DetroitDartworks/Flycore/DDW Angled Noidcore/ATNC - Pusher Guide.stl

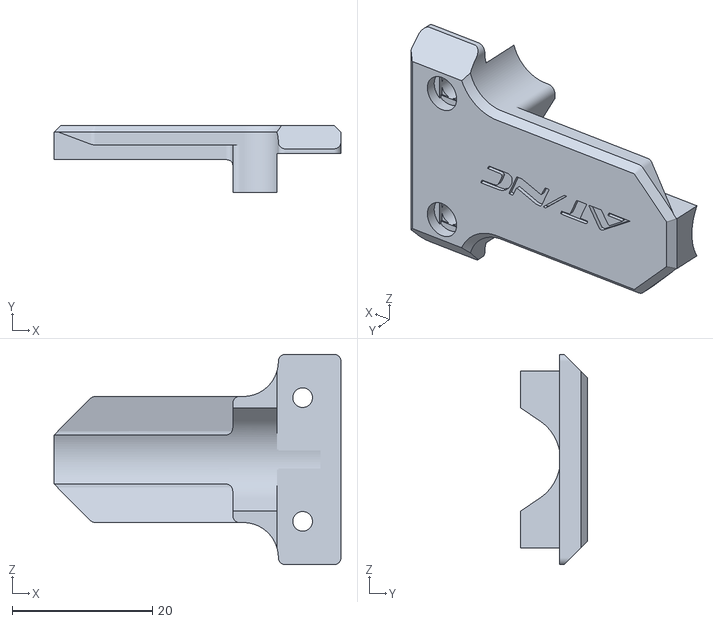
[picture p4: CAD file, 2025-03-11]
DDW Angled Noidcore/ATNC - Pusher Guide.stl
40.9 x 9.50 x 30.0
