DetroitDartworks/Flycore/FJZ05 Noidcore/FJZ05 Solenoid Flycore - HURR 33mm.stl

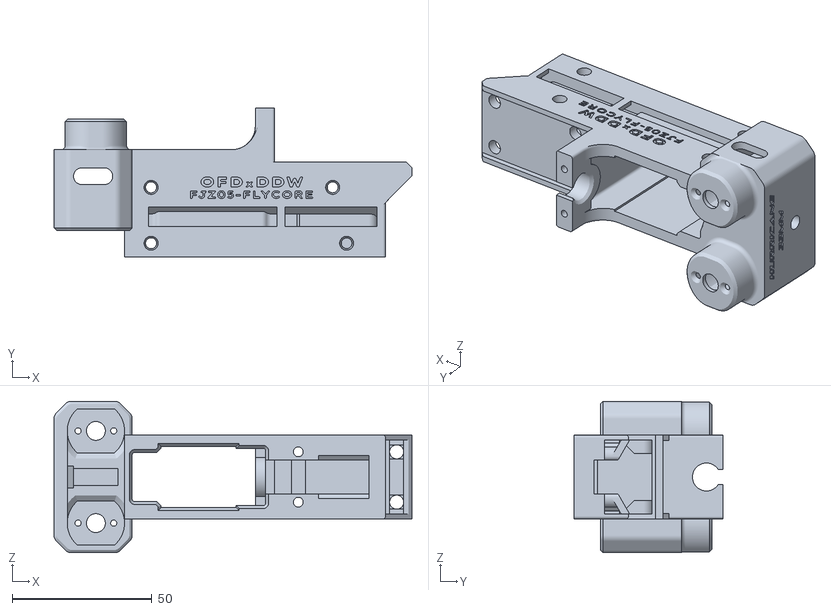
[picture p5: CAD file, 2024-03-11]
FJZ05 Noidcore/FJZ05 Solenoid Flycore - HURR 33mm.stl
128.2 x 53.5 x 54.2
