DetroitDartworks/Flycore/Gearcore v1/STEPs/Gearcore v1/GEARCORE_Trigger_Linkage_Reference.step

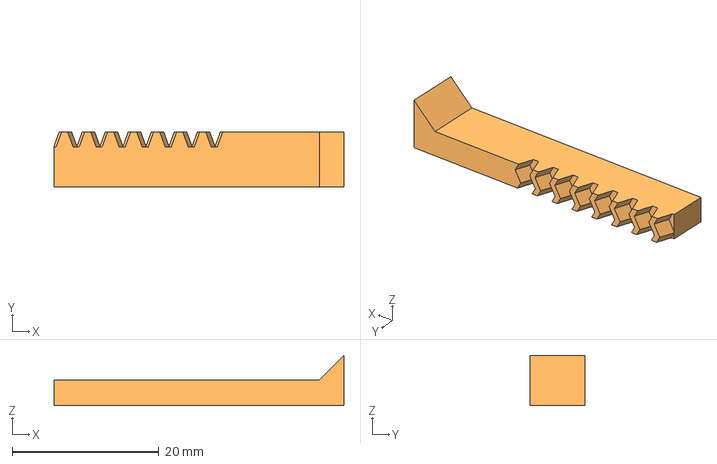
[picture p6: CAD file, 2025-07-15]
Gearcore v1/STEPs/Gearcore v1/GEARCORE_Trigger_Linkage_Reference.step
39.6 x 7.47 x 6.82 mm
