DetroitDartworks/Flycore/Gearcore v1/STLs/Gearcore v1/GearCore v1 - OFD_DDW_GEARCORE_STRAIGHT_NGALE_19.8MM_V1.stl

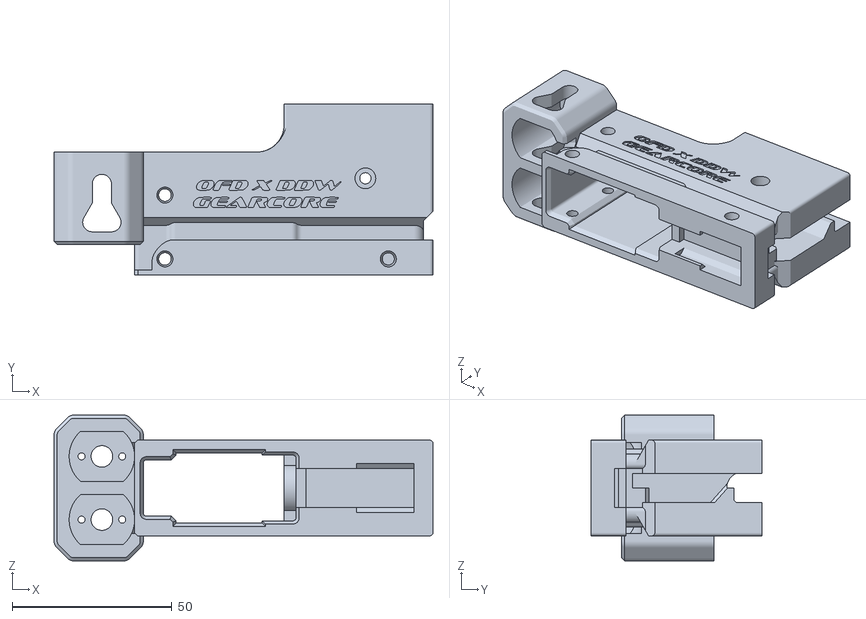
[picture p7: CAD file, 2025-07-15]
Gearcore v1/STLs/Gearcore v1/GearCore v1 - OFD_DDW_GEARCORE_STRAIGHT_NGALE_19.8MM_V1.stl
118.8 x 53.5 x 45.7
