DetroitDartworks/Flycore/Kodachi Flycore Dart Guides/Kodachi Flycore_Pusher_Guide_Straight_V1.stl

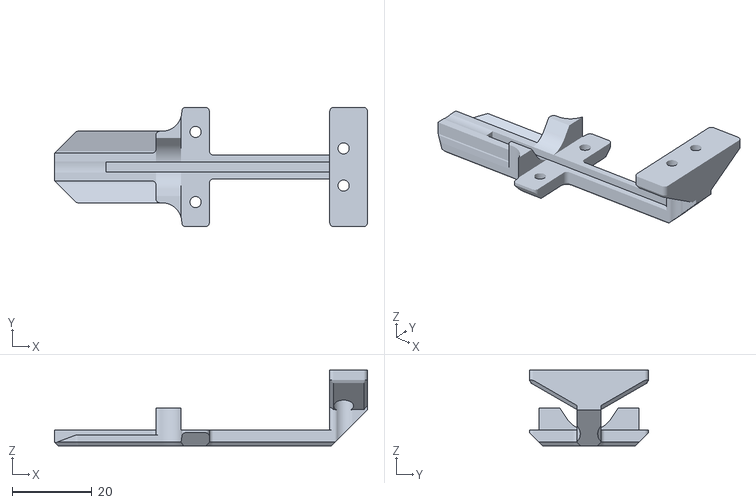
[picture p8: CAD file, 2024-03-11]
Kodachi Flycore Dart Guides/Kodachi Flycore_Pusher_Guide_Straight_V1.stl
78.7 x 30.0 x 19.0
