DetroitDartworks/Flycore/Gearcore v1/STEPs/Gearcore v1/Straight_Mag_Release_V1.STEP

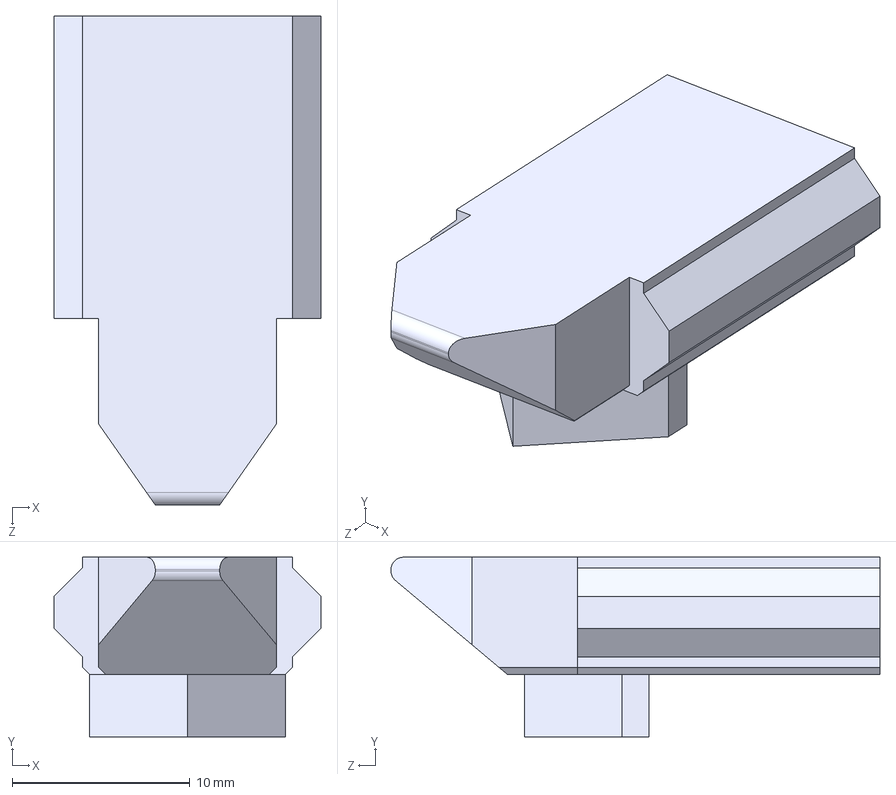
[picture p10: CAD file, 2025-07-15]
Gearcore v1/STEPs/Gearcore v1/Straight_Mag_Release_V1.STEP
15.0 x 10.1 x 27.5 mm
