DetroitDartworks/Flycore/Gearcore v1/STLs/Gearcore v1/GearCore v1 - OFD_DDW_GEARCORE_STRAIGHT_TRACEUR_25MM_V1.stl

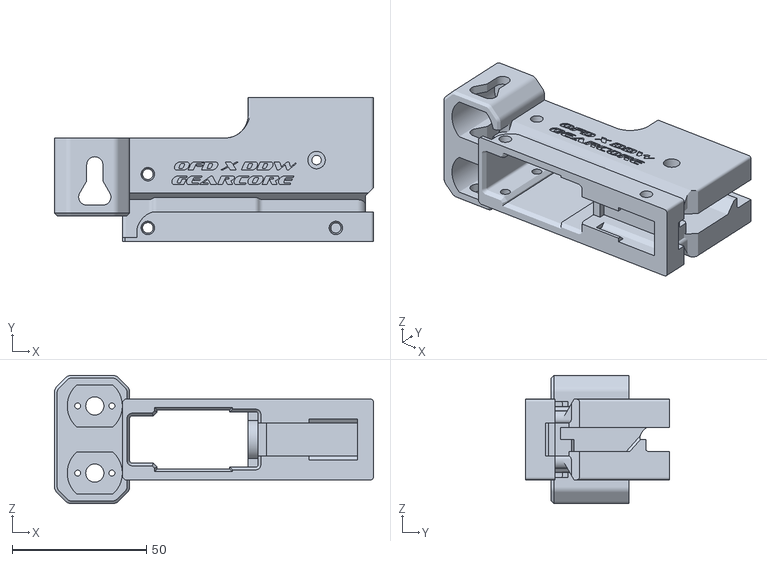
[picture p11: CAD file, 2025-07-15]
Gearcore v1/STLs/Gearcore v1/GearCore v1 - OFD_DDW_GEARCORE_STRAIGHT_TRACEUR_25MM_V1.stl
118.8 x 53.5 x 47.7
