DetroitDartworks/Flycore/DDW Angled Noidcore/ATNC - Neutron Pusher Nub.stl

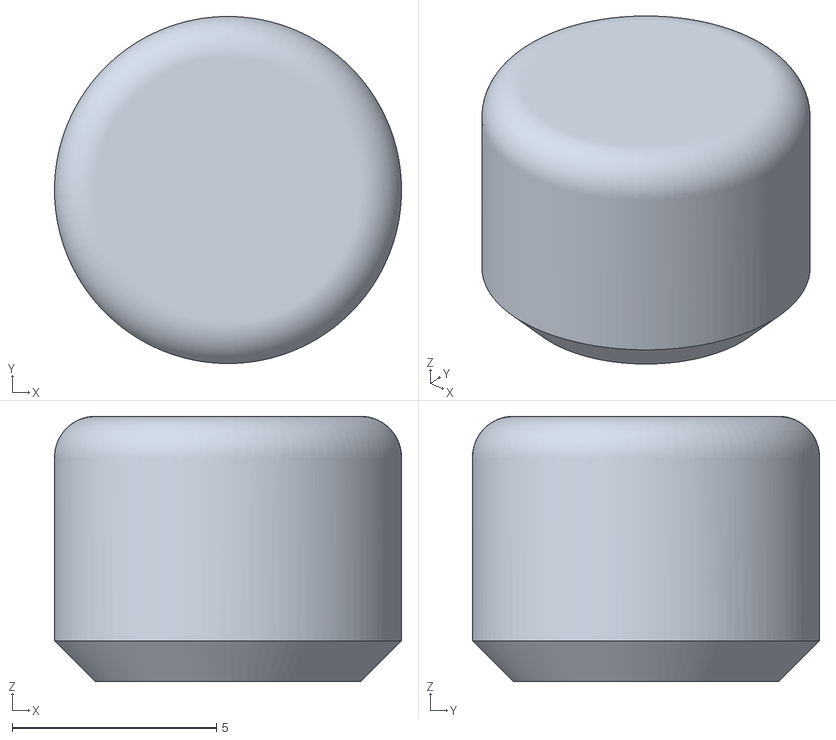
[picture p13: CAD file, 2025-03-11]
DDW Angled Noidcore/ATNC - Neutron Pusher Nub.stl
8.50 x 8.50 x 6.50
