DetroitDartworks/Flycore/Gearcore v1/STEPs/Gearcore v1/GEARCORE_Dart_Guide.step

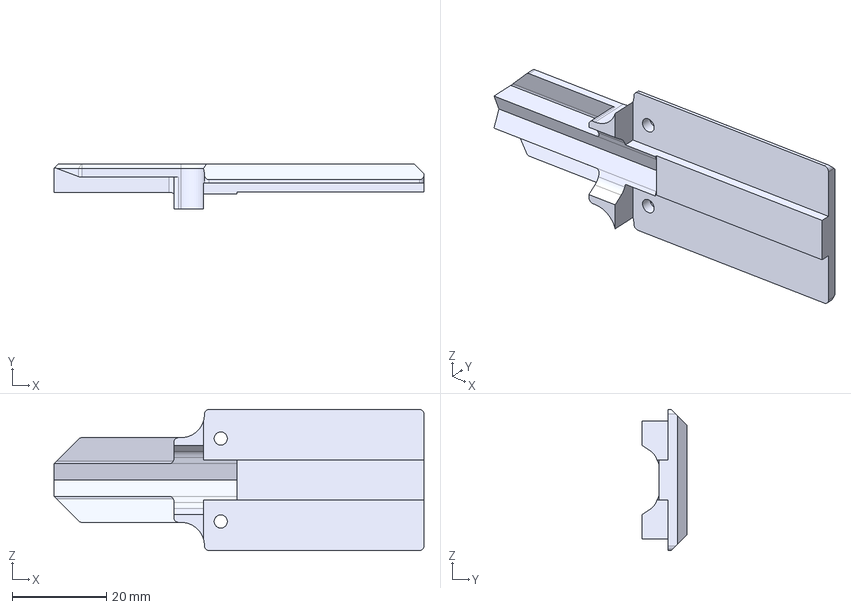
[picture p14: CAD file, 2025-07-15]
Gearcore v1/STEPs/Gearcore v1/GEARCORE_Dart_Guide.step
78.7 x 9.50 x 30.0 mm
