DetroitDartworks/Flycore/Kodachi Flycore Dart Guides/Kodachi NOIDCORE_Pusher_Guide_High_Straight_V1.stl

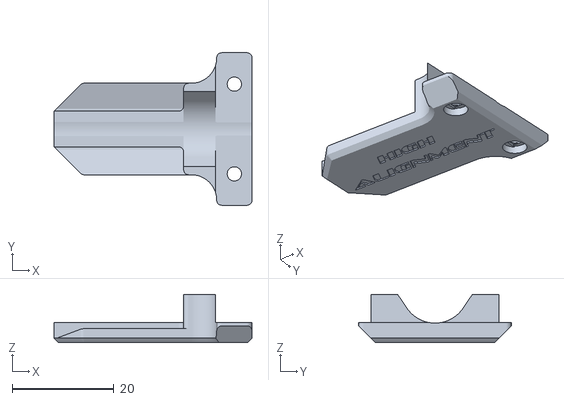
[picture p15: CAD file, 2024-03-11]
Kodachi Flycore Dart Guides/Kodachi NOIDCORE_Pusher_Guide_High_Straight_V1.stl
38.9 x 30.0 x 9.50
