DetroitDartworks/Flycore/DDW Angled Noidcore/Angled Flycore Mag Detent - DDW Remix.stl

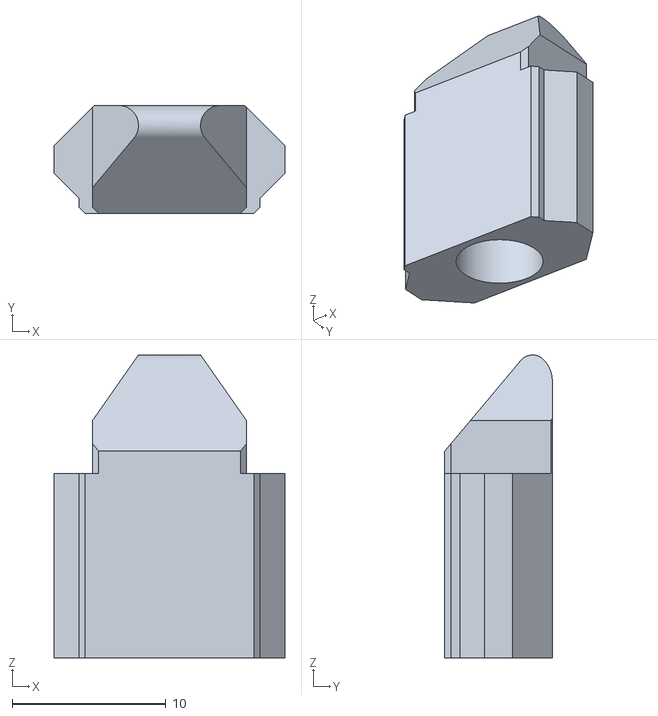
[picture p16: CAD file, 2025-03-11]
DDW Angled Noidcore/Angled Flycore Mag Detent - DDW Remix.stl
15.0 x 7.00 x 19.7
