DetroitDartworks/Flycore/FJZ05 Noidcore/FJZ05 Solenoid Flycore - FTW 22.5mm.stl

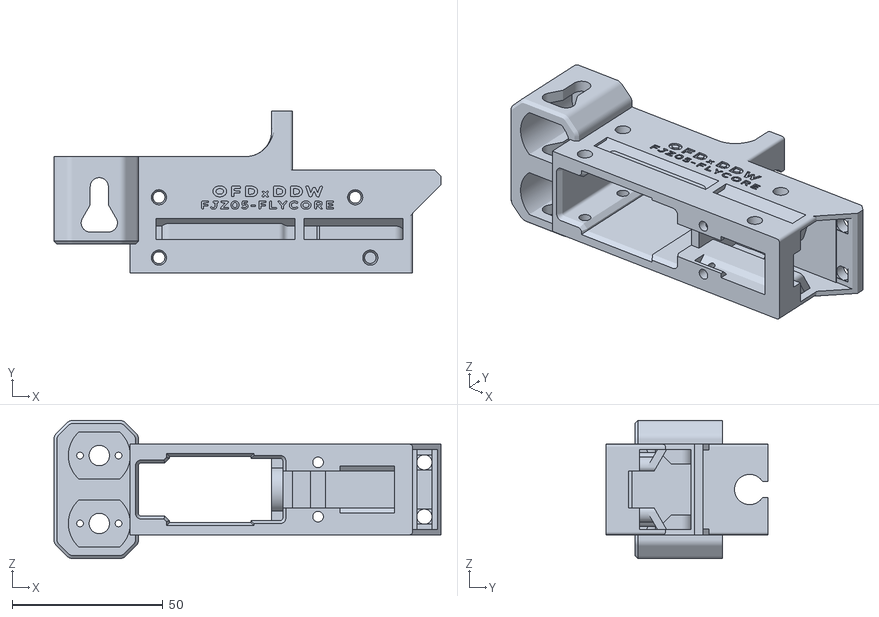
[picture p17: CAD file, 2024-03-11]
FJZ05 Noidcore/FJZ05 Solenoid Flycore - FTW 22.5mm.stl
128.2 x 53.5 x 45.7
