DetroitDartworks/Flycore/Gearcore v1/STEPs/Gearcore v1/GEARCORE_Pusher.step

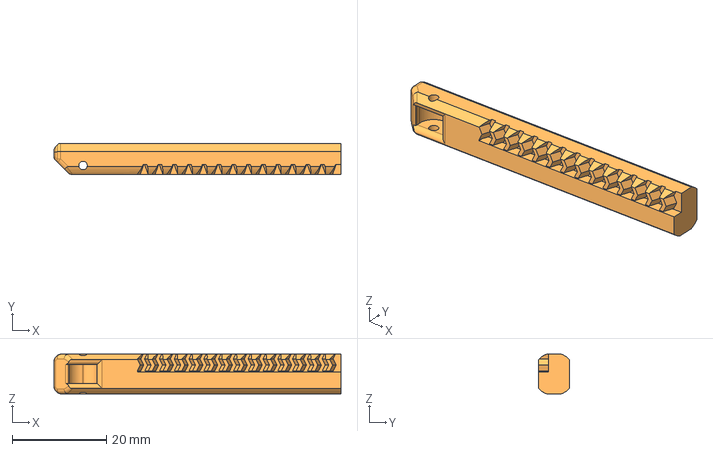
[picture p18: CAD file, 2025-07-15]
Gearcore v1/STEPs/Gearcore v1/GEARCORE_Pusher.step
60.9 x 6.48 x 8.40 mm
