DetroitDartworks/Flycore/FJZ05 Noidcore/FJZ05Core Pusher Nub Low.stl

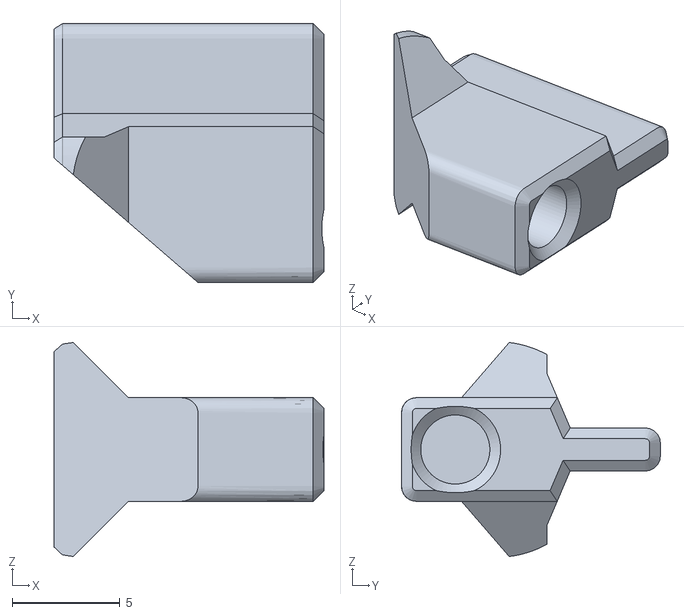
[picture p19: CAD file, 2024-03-11]
FJZ05 Noidcore/FJZ05Core Pusher Nub Low.stl
12.5 x 12.0 x 9.91
