DetroitDartworks/Flycore/Gearcore v1/STEPs/Gearcore v1/Straight_Mag_Detent_V1.STEP

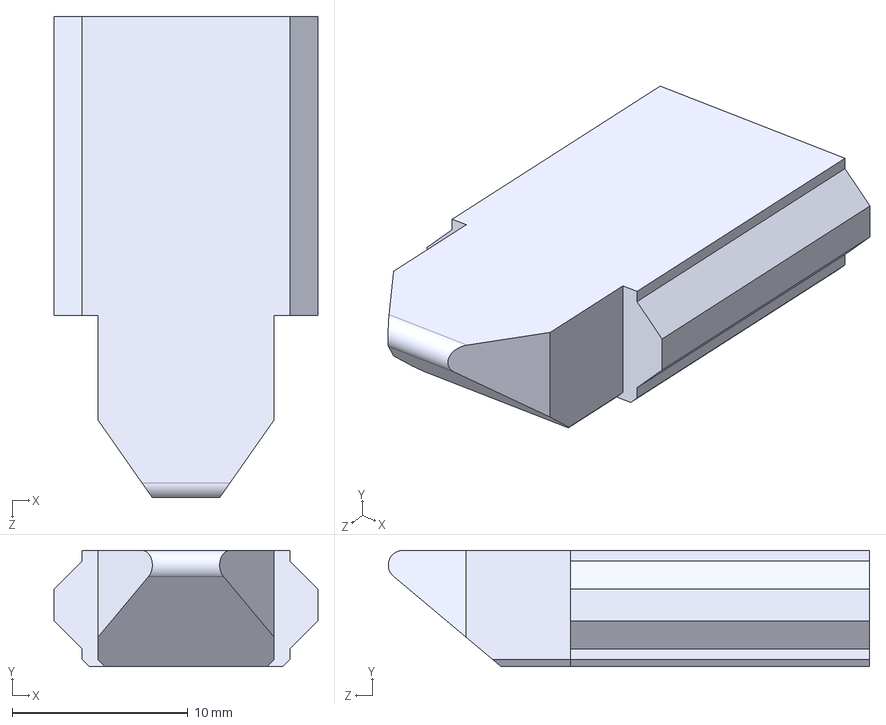
[picture p20: CAD file, 2025-07-15]
Gearcore v1/STEPs/Gearcore v1/Straight_Mag_Detent_V1.STEP
15.0 x 6.60 x 27.4 mm
