DetroitDartworks/Flycore/Gearcore v1/STLs/Gearcore v1/GEARCORE - Pusher Roller.stl

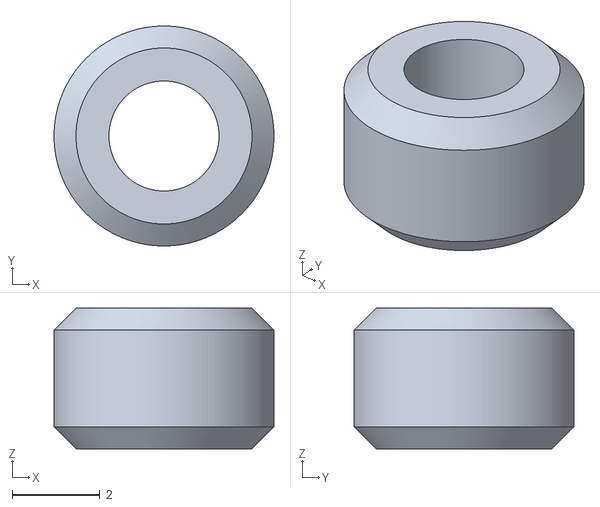
[picture p21: CAD file, 2025-07-15]
Gearcore v1/STLs/Gearcore v1/GEARCORE - Pusher Roller.stl
5.00 x 5.00 x 3.20
