DetroitDartworks/Flycore/Gearcore v1/STLs/Gearcore v1/GEARCORE - Gear - 3to1.stl

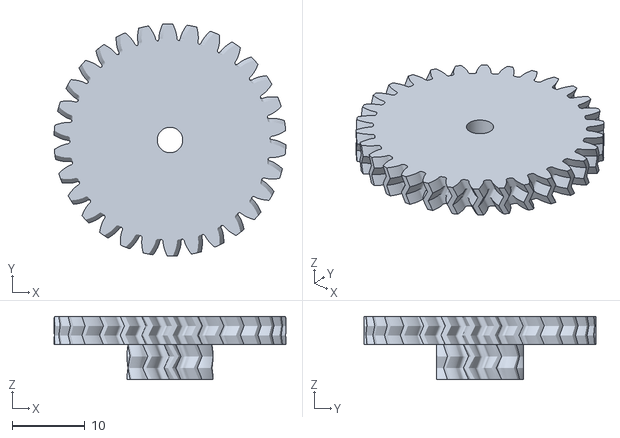
[picture p22: CAD file, 2025-07-15]
Gearcore v1/STLs/Gearcore v1/GEARCORE - Gear - 3to1.stl
32.0 x 32.0 x 8.70
