DetroitDartworks/Flycore/Gearcore v1/STEPs/Gearcore v1/OFD_DDW_GEARCORE_STRAIGHT_HURR_32.5MM_V2.step

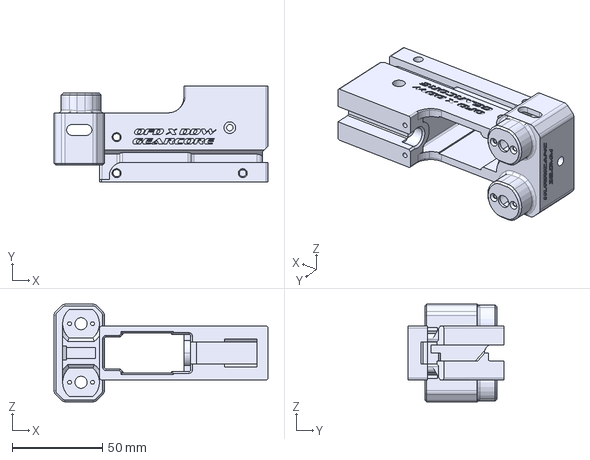
[picture p23: CAD file, 2025-07-15]
Gearcore v1/STEPs/Gearcore v1/OFD_DDW_GEARCORE_STRAIGHT_HURR_32.5MM_V2.step
118.8 x 53.5 x 54.2 mm
