DetroitDartworks/Flycore/DDW Angled Noidcore/STEPs/ATNC - 22mm FTW.step

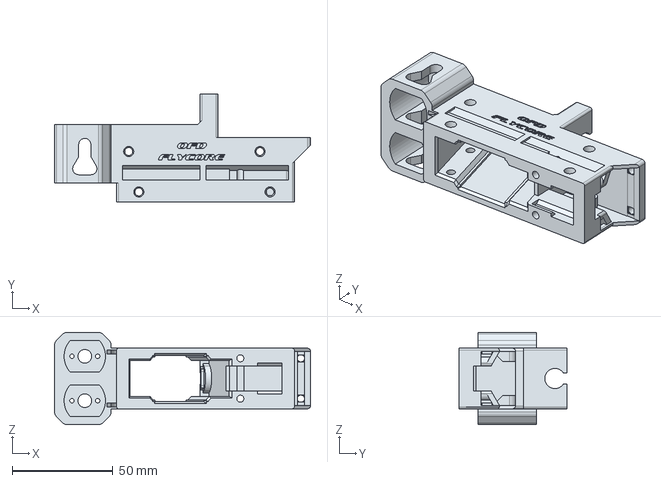
[picture p24: CAD file, 2025-03-11]
DDW Angled Noidcore/STEPs/ATNC - 22mm FTW.step
126.8 x 53.5 x 45.7 mm
