DetroitDartworks/Flycore/Gearcore v1/STLs/Gearcore v1/GEARCORE TOP LOAD PUSHER GUIDE.stl

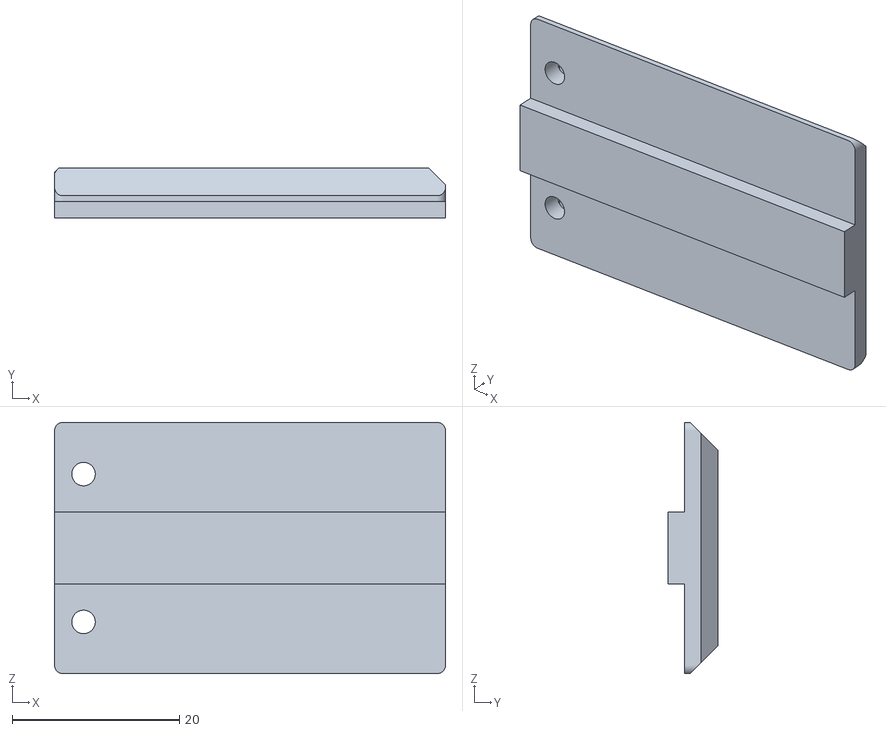
[picture p25: CAD file, 2025-07-15]
Gearcore v1/STLs/Gearcore v1/GEARCORE TOP LOAD PUSHER GUIDE.stl
46.7 x 5.96 x 30.0
