DetroitDartworks/Flycore/DDW Angled Noidcore/STEPs/ATNC - 32.5mm Hurr.step

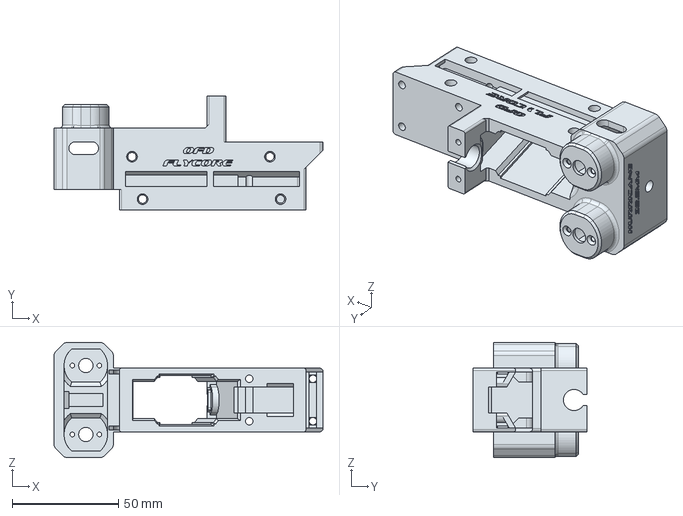
[picture p26: CAD file, 2025-03-11]
DDW Angled Noidcore/STEPs/ATNC - 32.5mm Hurr.step
126.8 x 53.5 x 54.2 mm
