DetroitDartworks/Flycore/FJZ05 Noidcore/Kodachi FJZ05 Noidcore Pusher Guide Low.stl

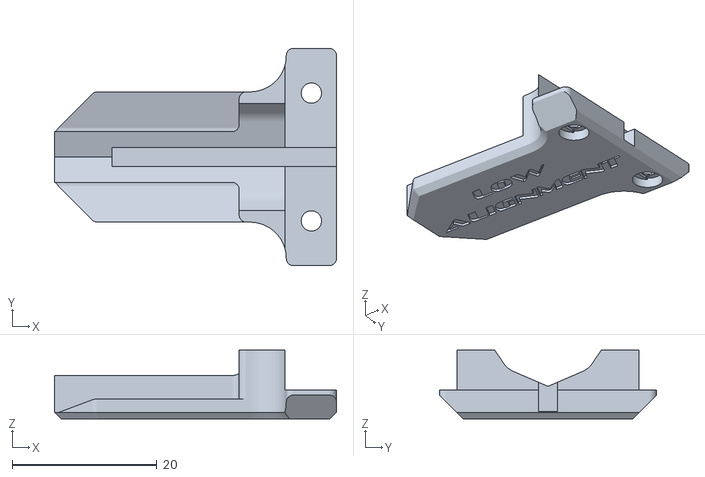
[picture p27: CAD file, 2024-03-11]
FJZ05 Noidcore/Kodachi FJZ05 Noidcore Pusher Guide Low.stl
38.9 x 30.0 x 9.50
