DetroitDartworks/Flycore/DDW Angled Noidcore/STEPs/ATNC - 25mm Traceur.step

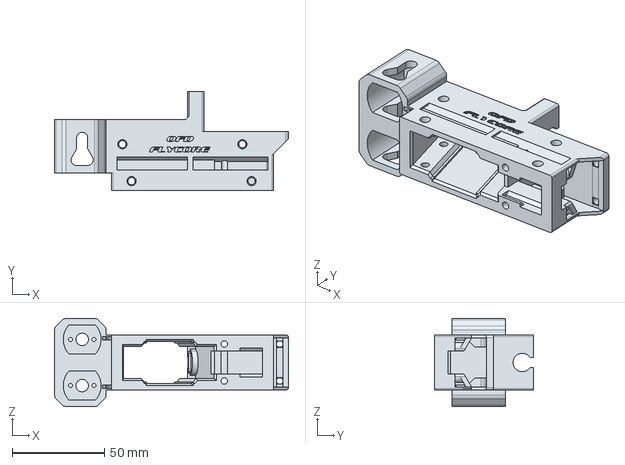
[picture p28: CAD file, 2025-03-11]
DDW Angled Noidcore/STEPs/ATNC - 25mm Traceur.step
126.8 x 53.5 x 47.7 mm
